shreaypatel/splitKey/PCB/pcbEditorCompleteWiring.png

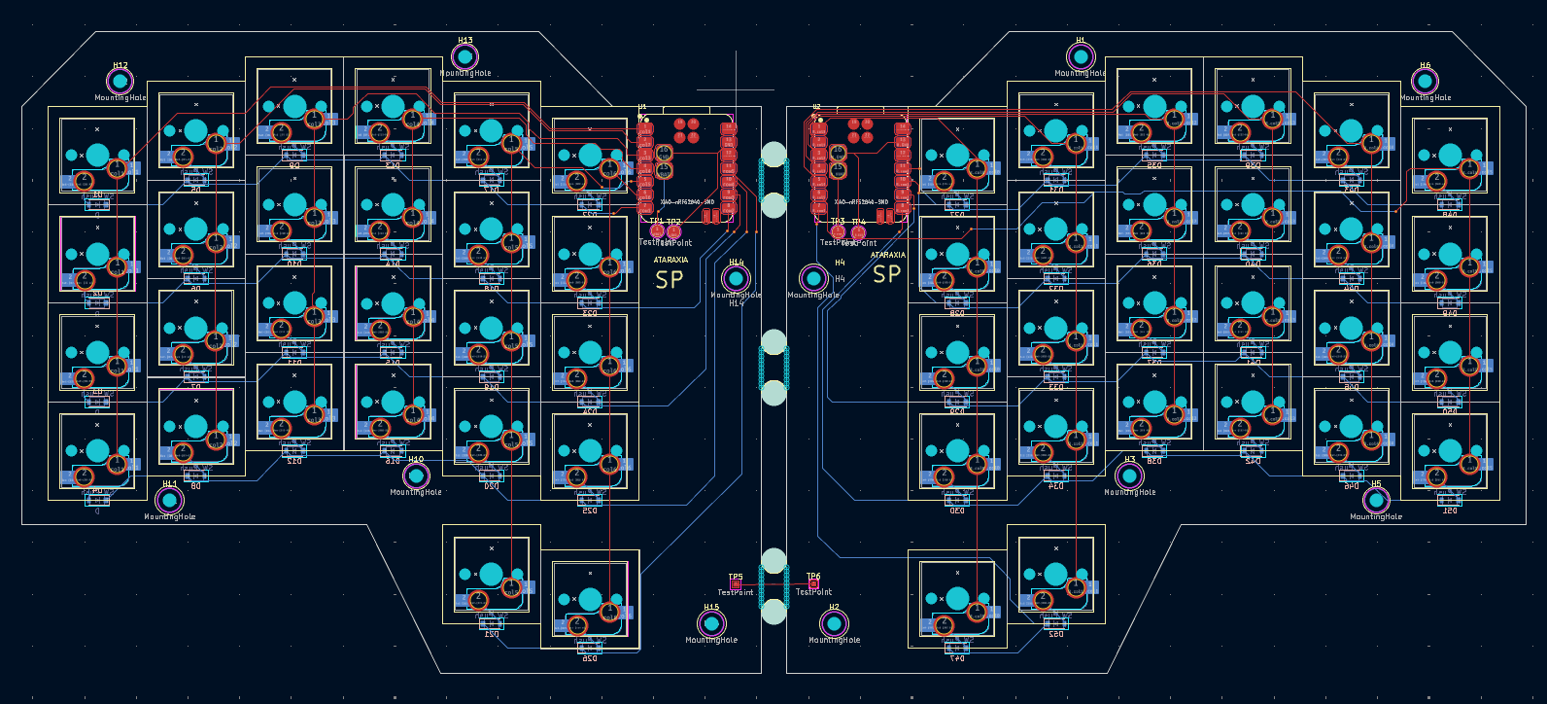
PCB/pcbEditorCompleteWiring.png
